CombatCovid/OxyGEN-Ventilators/docs/img/5 mm/71f6ea7c-f07a-48c2-86b9-0ffa20c125fe.jpeg

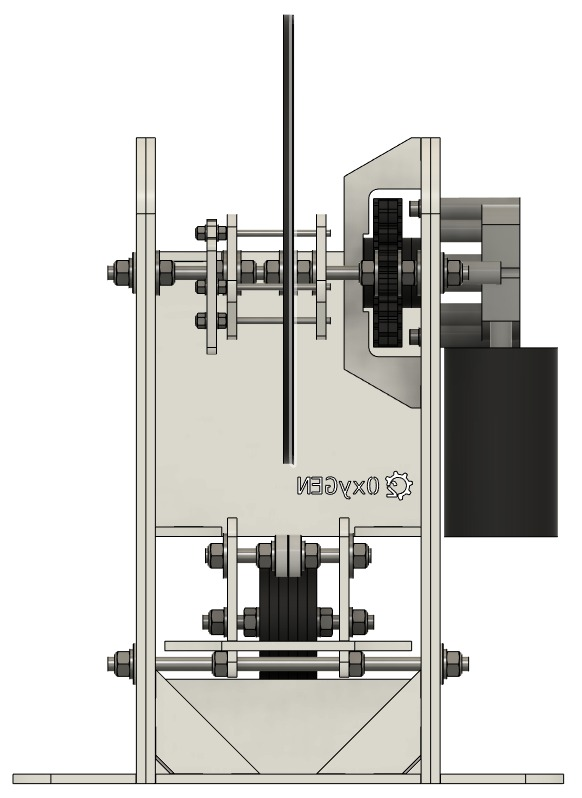
docs/img/5 mm/71f6ea7c-f07a-48c2-86b9-0ffa20c125fe.jpeg
