CombatCovid/OxyGEN-Ventilators/docs/img/5 mm/628c36c9-1eaf-4945-878f-27b9a3d66050.jpeg

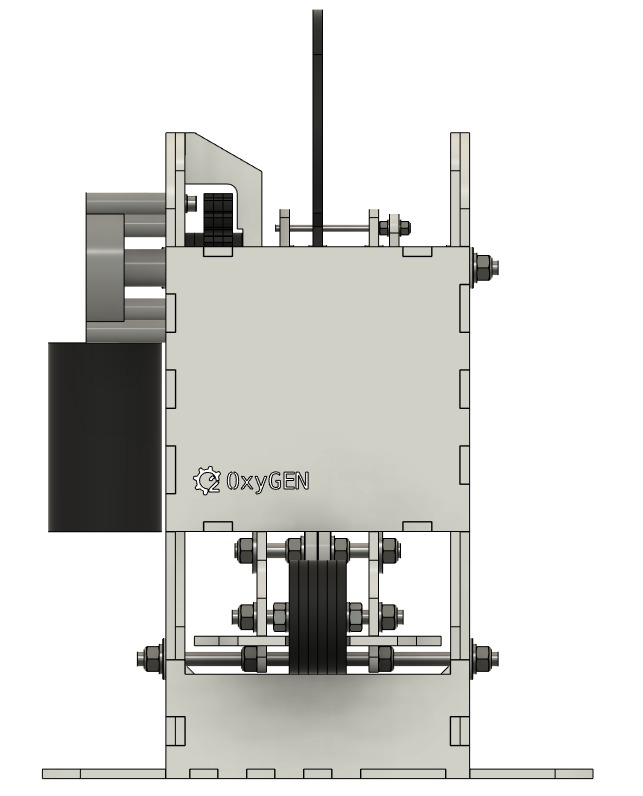
docs/img/5 mm/628c36c9-1eaf-4945-878f-27b9a3d66050.jpeg
