CombatCovid/OxyGEN-Ventilators/docs/img/5 mm/67442de0-a628-4195-af0d-b7cb26ab55f8.jpeg

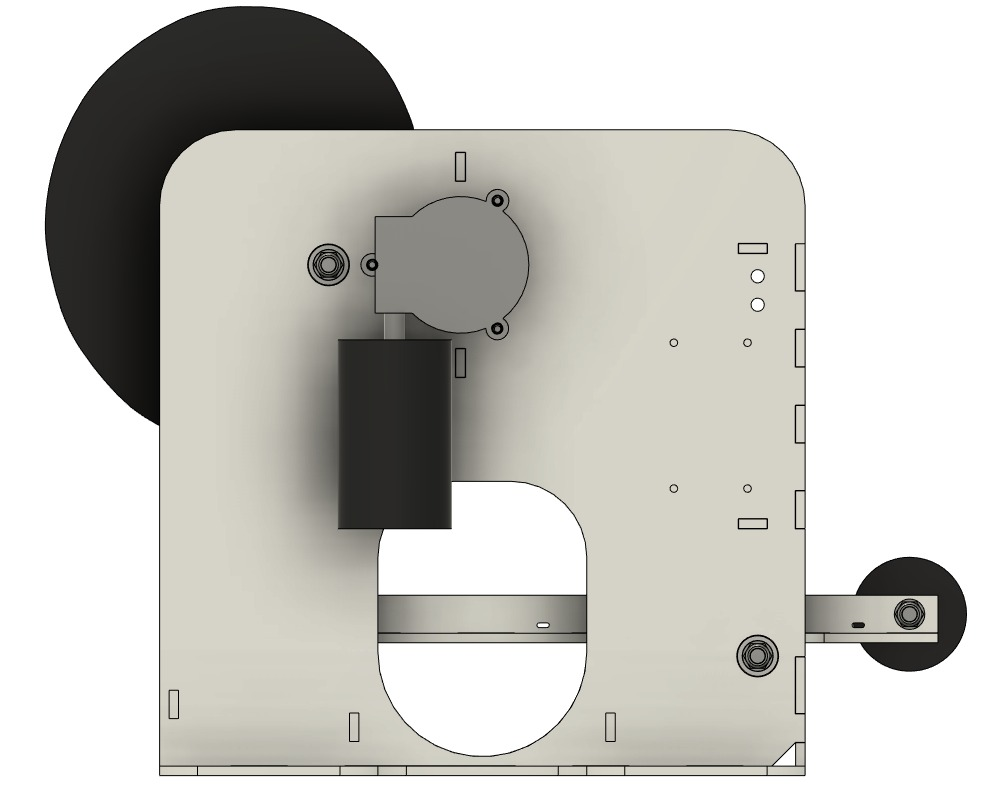
docs/img/5 mm/67442de0-a628-4195-af0d-b7cb26ab55f8.jpeg
