CombatCovid/OxyGEN-Ventilators/docs/img/5 mm/f347e17a-e1d2-4af8-affd-06b3623857e8.jpeg

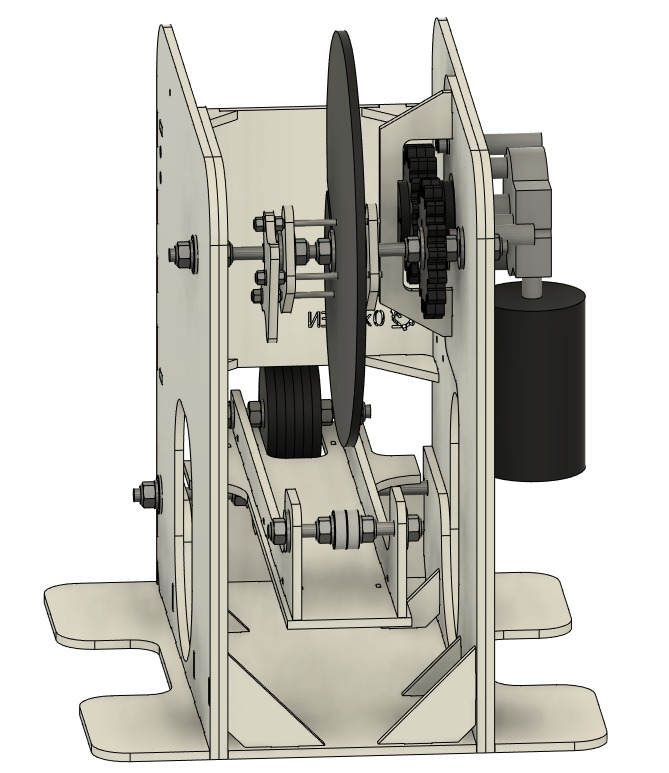
docs/img/5 mm/f347e17a-e1d2-4af8-affd-06b3623857e8.jpeg
