CombatCovid/OxyGEN-Ventilators/src/accessories/picture.jpeg

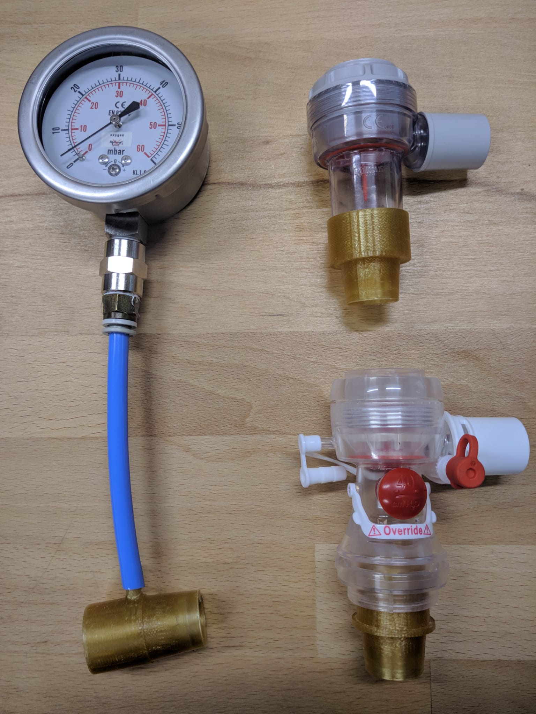
src/accessories/picture.jpeg
