CombatCovid/OxyGEN-Ventilators/src/Matlab Files/V8/1_1_Cycle_83_205_50_V8.jpg

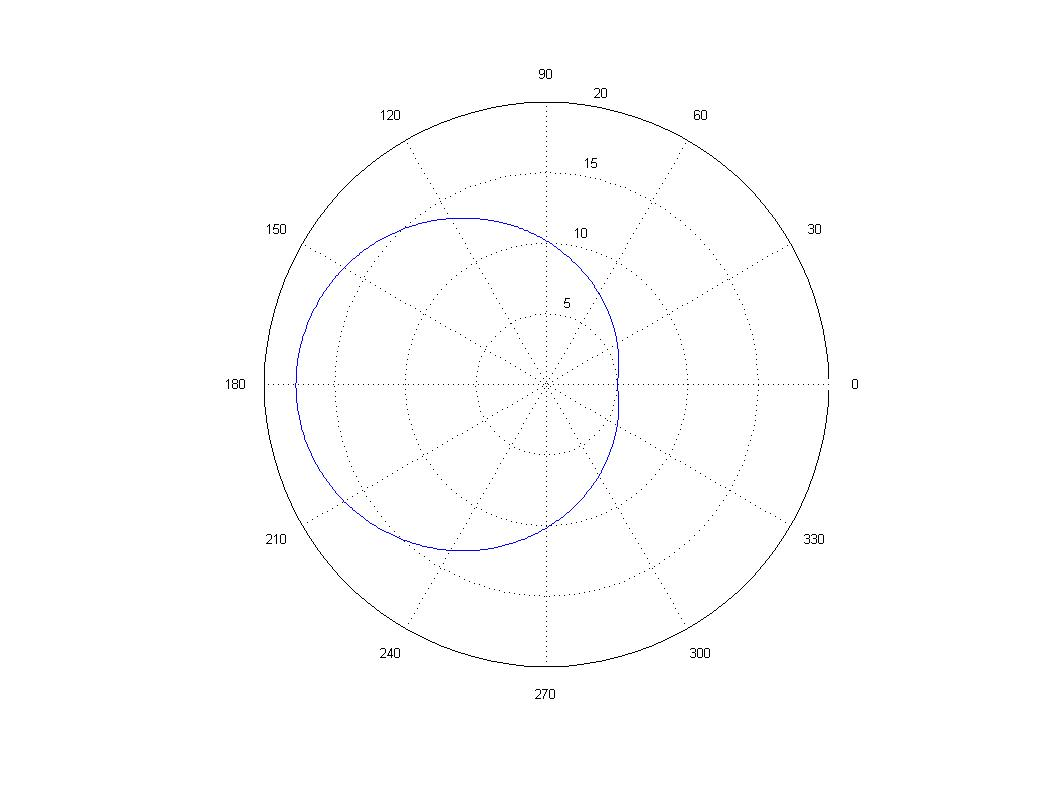
src/Matlab Files/V8/1_1_Cycle_83_205_50_V8.jpg
