CombatCovid/OxyGEN-Ventilators/src/Matlab Files/V8/1_2_Cycle_77_205_50_V8.jpg

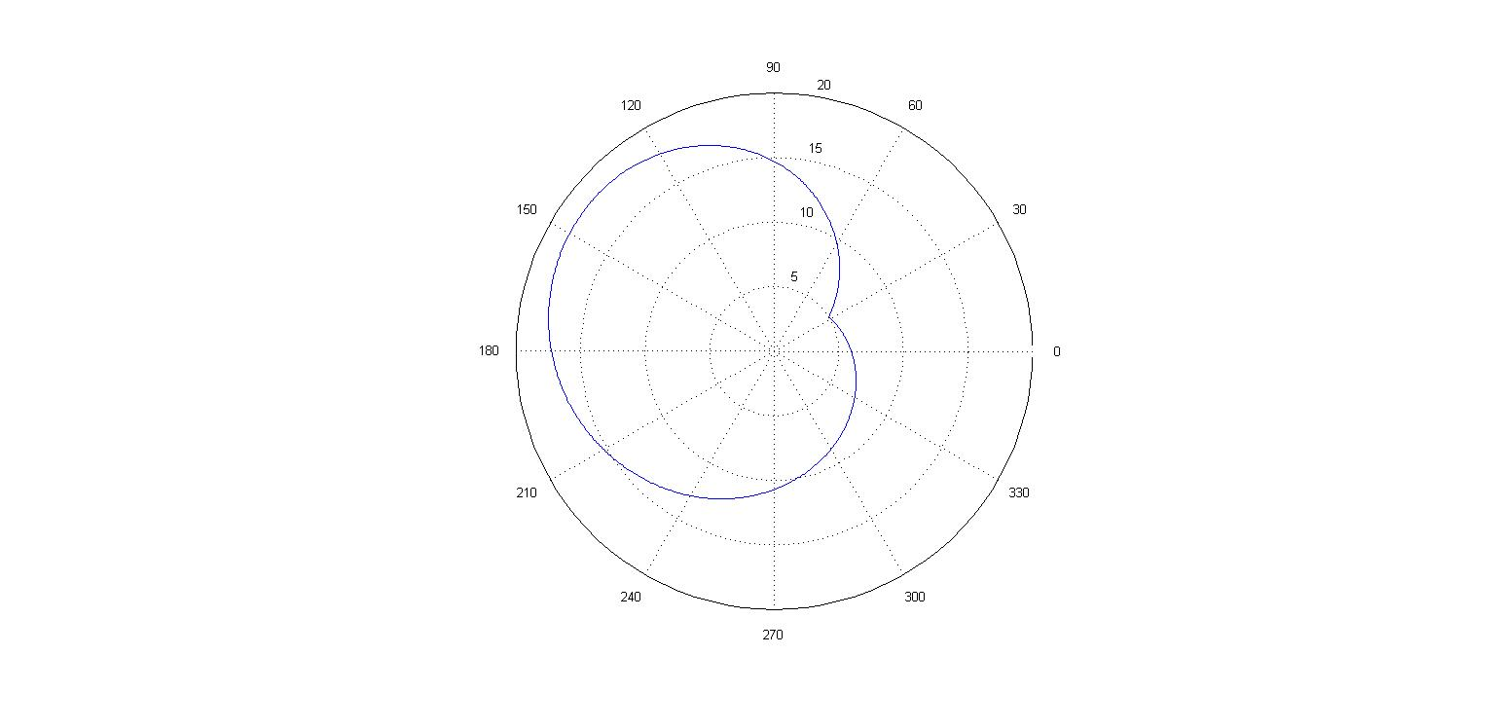
src/Matlab Files/V8/1_2_Cycle_77_205_50_V8.jpg
