CombatCovid/OxyGEN-Ventilators/src/Matlab Files/V8/1_3_Cycle_65_205_50_V8.jpg

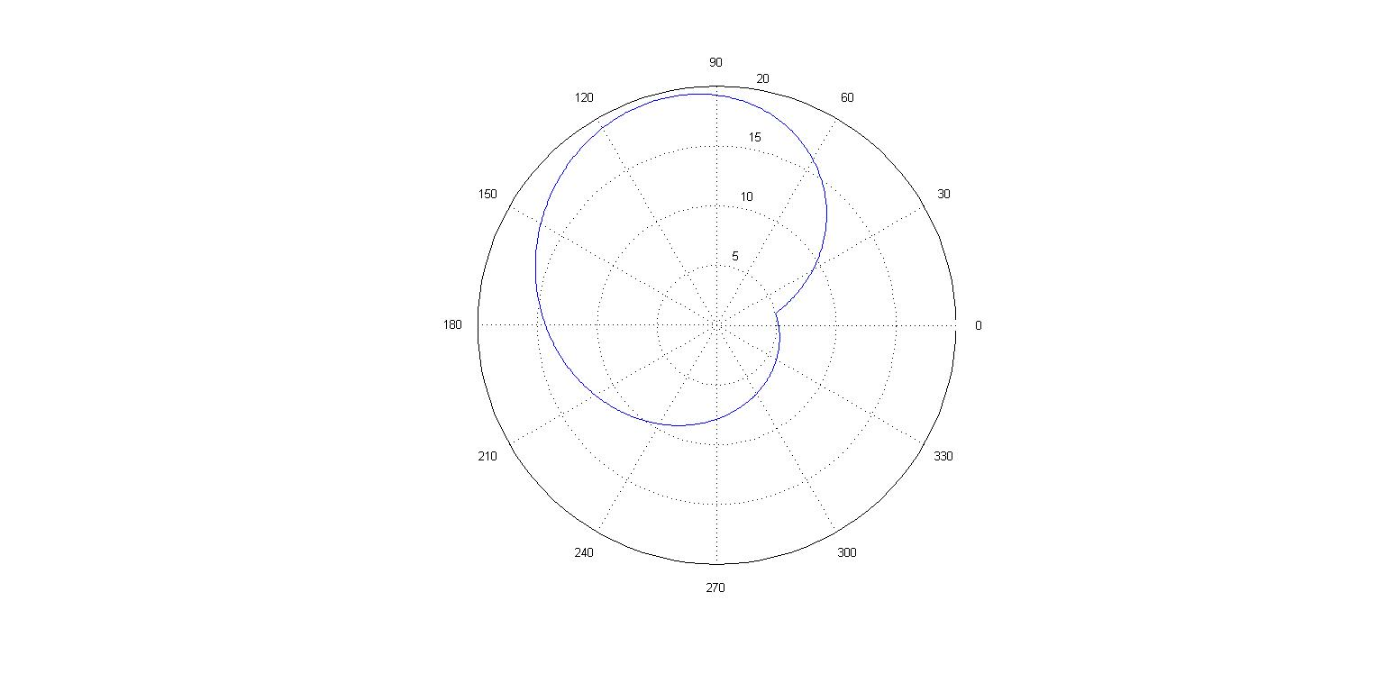
src/Matlab Files/V8/1_3_Cycle_65_205_50_V8.jpg
