CombatCovid/OxyGEN-Ventilators/src/Matlab Files/V8/1_3_Normalized_Breath_Cycle_V8.jpg

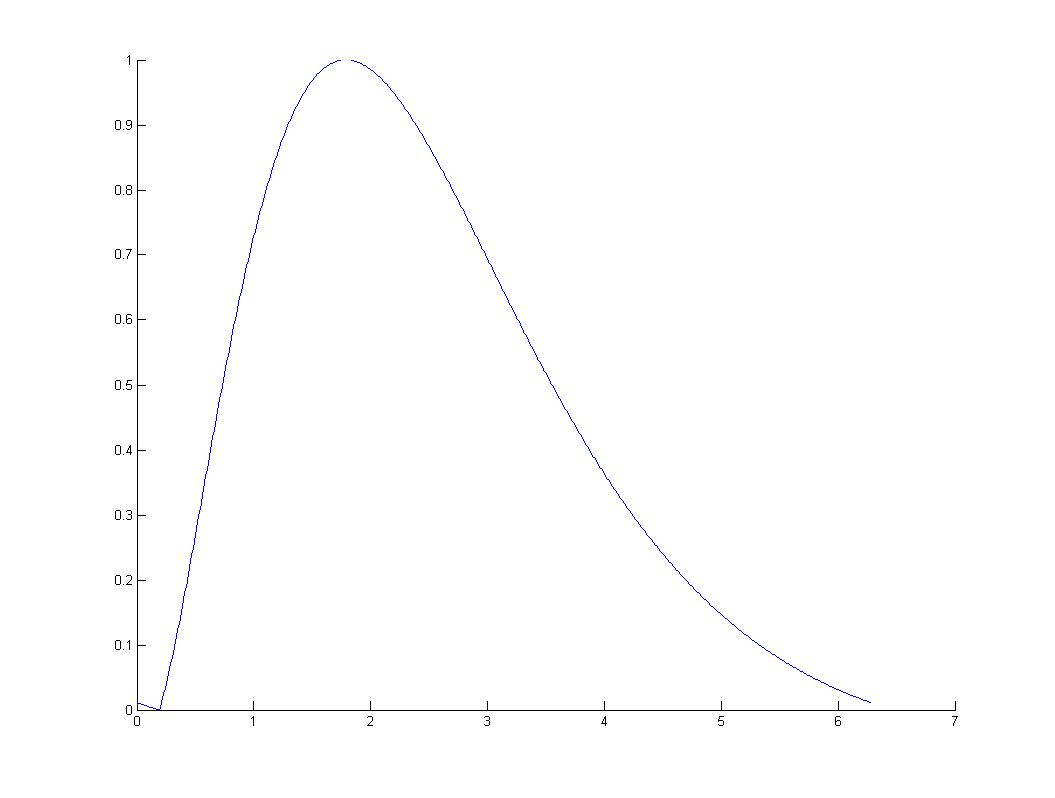
src/Matlab Files/V8/1_3_Normalized_Breath_Cycle_V8.jpg
