CombatCovid/OxyGEN-Ventilators/src/Matlab Files/V8/Positions_65_71_77_83_to_205_X238_Y264_V8.jpg

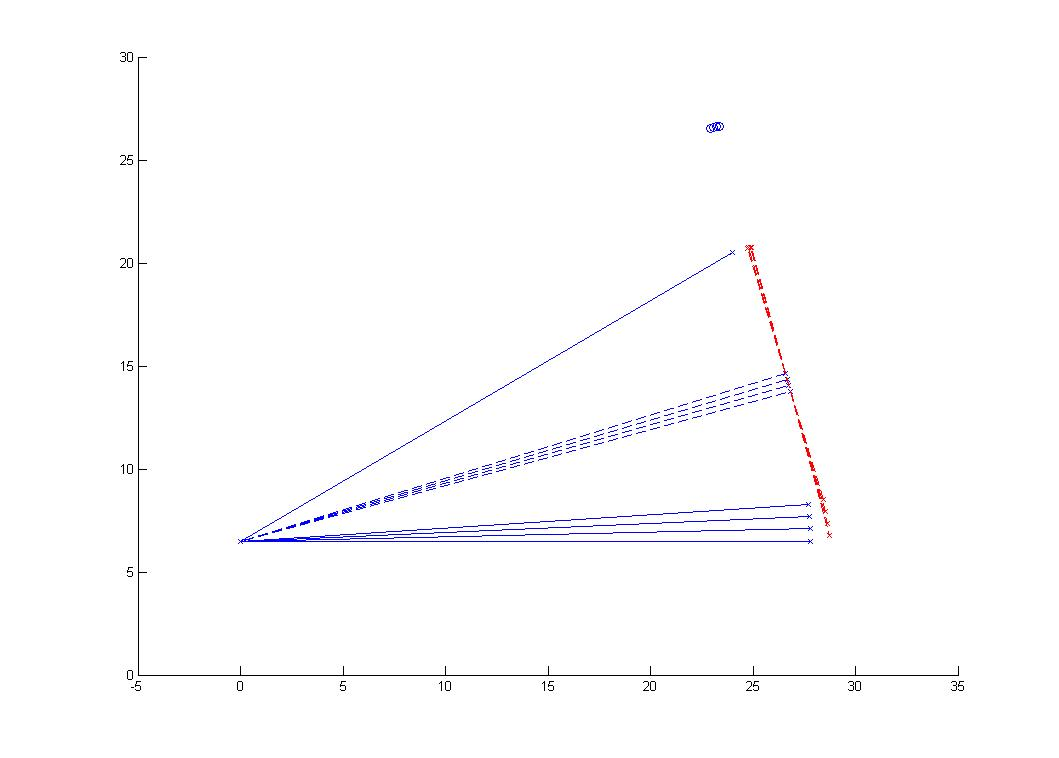
src/Matlab Files/V8/Positions_65_71_77_83_to_205_X238_Y264_V8.jpg
