CombatCovid/OxyGEN-Ventilators/src/OxyGEN-M_v5/OxyGEN-M_v5 5mm/STEP/Oxygen Maker Leva2 Entallada.step

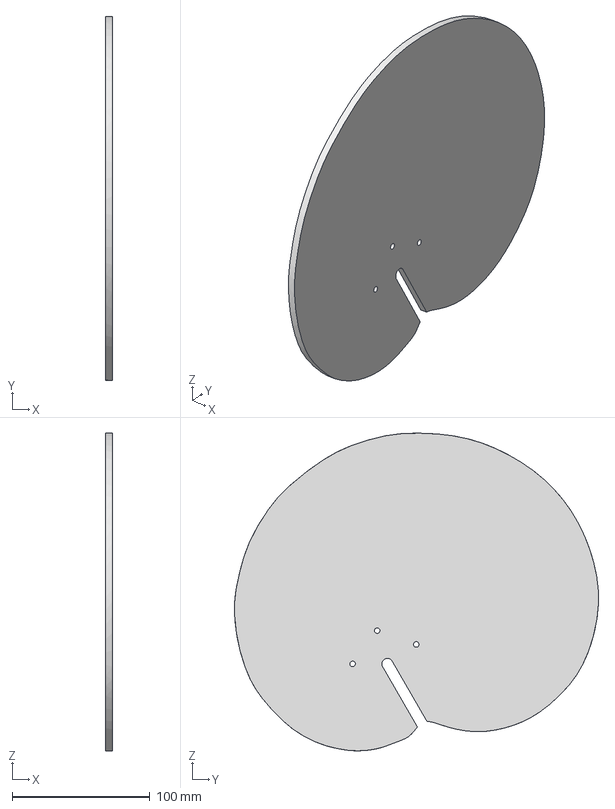
[picture p36: CAD file, 2020-04-10]
src/OxyGEN-M_v5/OxyGEN-M_v5 5mm/STEP/Oxygen Maker Leva2 Entallada.step
5.00 x 263.9 x 230.3 mm
