CombatCovid/OxyGEN-Ventilators/src/OxyGEN-M_v5/OxyGEN-M_v5 5mm/STEP/Oxygen Maker Leva3 Entallada.step

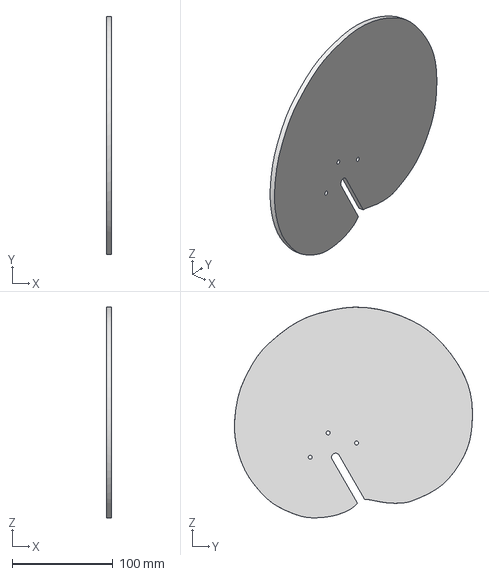
[picture p37: CAD file, 2020-04-10]
src/OxyGEN-M_v5/OxyGEN-M_v5 5mm/STEP/Oxygen Maker Leva3 Entallada.step
5.00 x 236.6 x 209.4 mm
