CombatCovid/OxyGEN-Ventilators/src/OxyGEN-M_v5/OxyGEN-M_v5 5mm/STEP/Oxygen Maker Tope Coupling.step

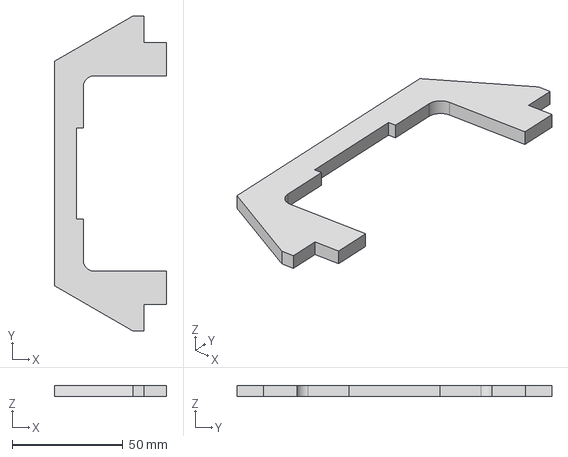
[picture p38: CAD file, 2020-04-10]
src/OxyGEN-M_v5/OxyGEN-M_v5 5mm/STEP/Oxygen Maker Tope Coupling.step
50.6 x 142.3 x 5.00 mm
