CombatCovid/OxyGEN-Ventilators/src/OxyGEN-M_v5/OxyGEN-M_v5 5mm/STEP/Oxygen Maker Lateral Izquierdo Interior.step

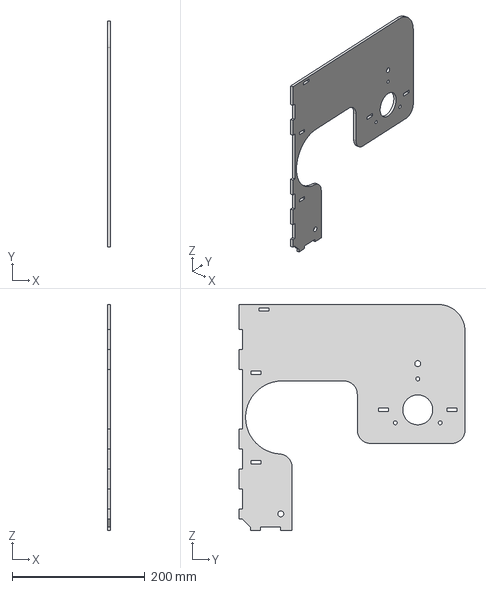
[picture p40: CAD file, 2020-04-10]
src/OxyGEN-M_v5/OxyGEN-M_v5 5mm/STEP/Oxygen Maker Lateral Izquierdo Interior.step
5.00 x 340.2 x 340.0 mm
