CombatCovid/OxyGEN-Ventilators/src/OxyGEN-M_v5/OxyGEN-M_v5 5mm/STEP/Oxygen Maker Frontal Inferior Exterior.step

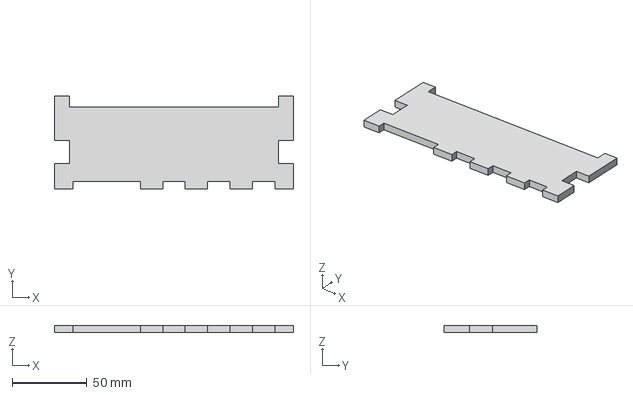
[picture p43: CAD file, 2020-04-10]
src/OxyGEN-M_v5/OxyGEN-M_v5 5mm/STEP/Oxygen Maker Frontal Inferior Exterior.step
160.0 x 62.5 x 5.00 mm
