CombatCovid/OxyGEN-Ventilators/src/OxyGEN-M_v5/OxyGEN-M_v5 5mm/Technical drawings/LATERAL DERECHO EXTERIOR.PDF

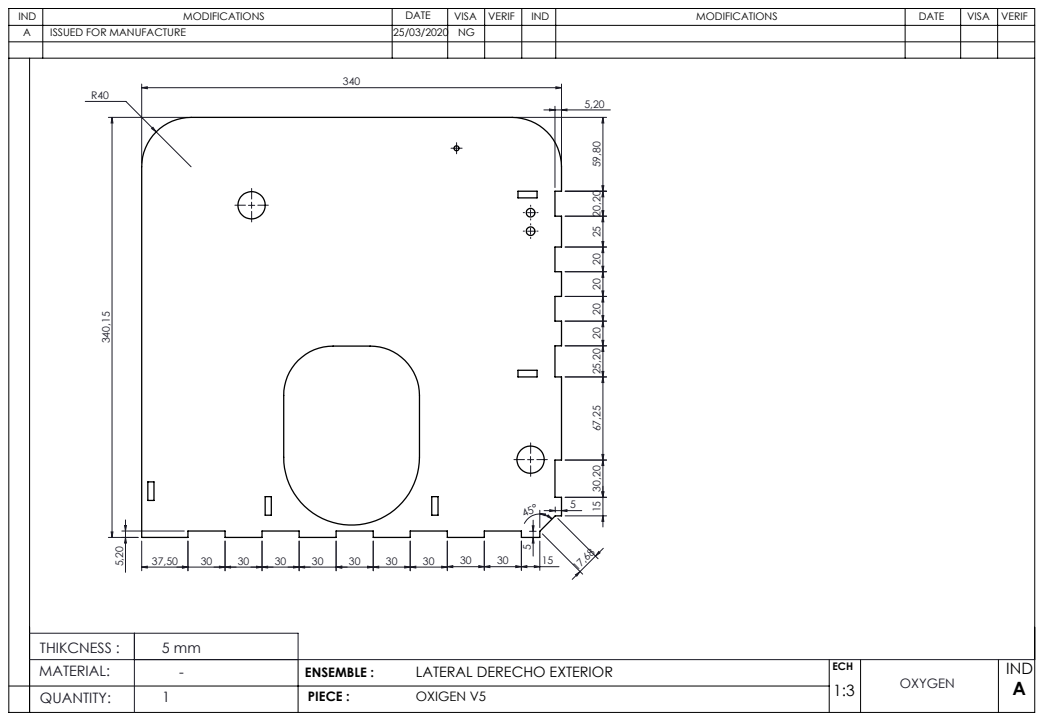
[picture p74: page 1]

IND | MODIFICATIONS | DATE | VISA | VERIF | MODIFICATIONS | DATE | VISA | VERIF
A | ISSUED FOR MANUFACTURE | 25/03/2020 | NG

THIKCNESS : | 5 mm
MATERIAL: | - | ENSEMBLE : LATERAL DERECHO EXTERIOR | ECH 1:3 | OXYGEN | IND A
QUANTITY: | 1 | PIECE : OXIGEN V5

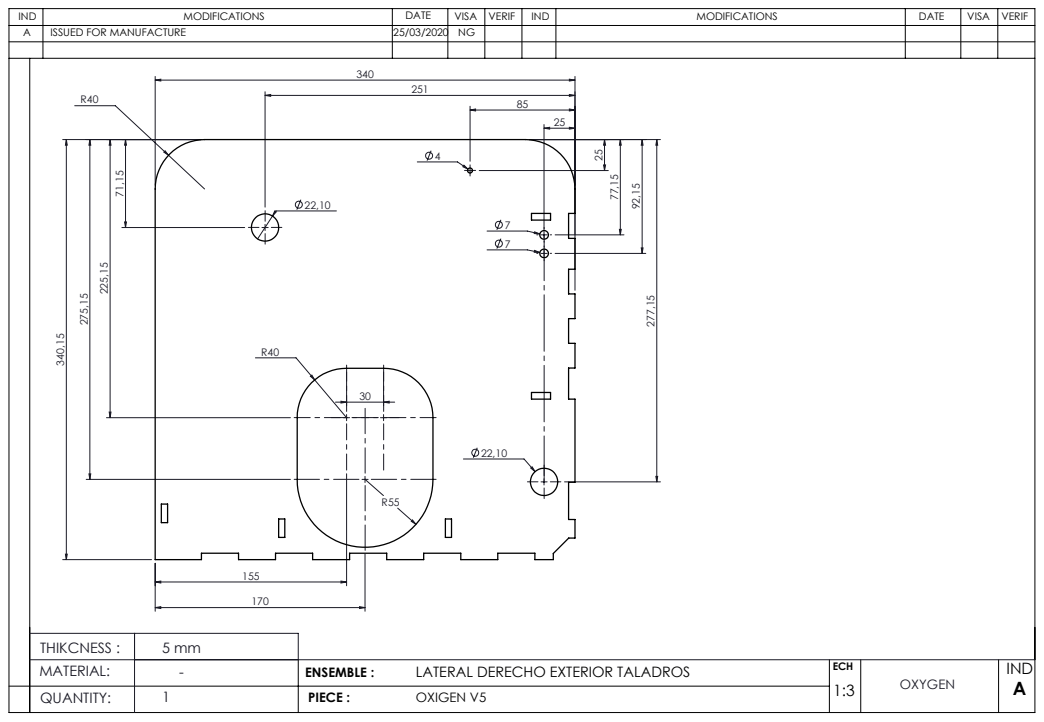
[picture p75: page 2]
ISSUED FOR MANUFACTURE

THIKCNESS : | 5 mm
MATERIAL: | - | ENSEMBLE : LATERAL DERECHO EXTERIOR TALADROS | ECH 1:3 | OXYGEN | IND

1 | PIECE :

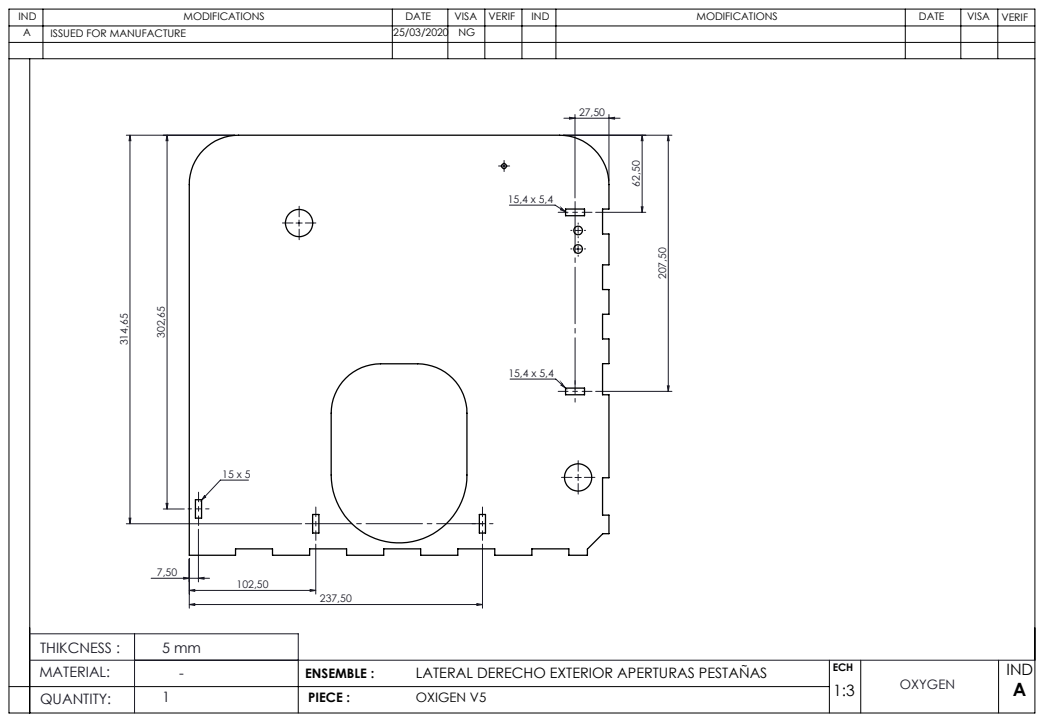
[picture p76: page 3]
ISSUED FOR MANUFACTURE

THIKCNESS : | 5 mm
MATERIAL: | - | ENSEMBLE : LATERAL DERECHO EXTERIOR APERTURAS PESTAÑAS | ECH 1:3 | OXYGEN | IND A

1 | PIECE :
